microchip-pic-avr-examples/pic16f17146-cold-plate-mplab-mcc/pic16f17146-cold-plate-mplab-mcc.X/compactPrint.c

#include "compactPrint.h"

#include <xc.h>
#include "mcc_generated_files/system/system.h"
#include "fanControl.h"
#include "measurements.h"
#include "settings.h"
#include "peltierControl.h"
#include "currentSense.h"

//Sends a string of text to the UART with no newline appended
void compactPrint_sendStringLiteral(const char* str)
{
    uint8_t index = 0;
    while (str[index] != '\0')
    {
        if (UART1_IsTxReady())
        {
            UART1_Write(str[index]);
            index++;
        }
    }
    
    //Wait for TX
    while (!UART1_IsTxDone());
}

//Sends a string of text to the UART with a newline appended.
void compactPrint_sendStringWithNewline(const char* str)
{
    compactPrint_sendStringLiteral(str);
    compactPrint_sendStringLiteral("\r\n");
}

//Sends a string + error code with a newline appended.
void compactPrint_sendErrorCode(const char* str, uint8_t err)
{
    char buffer[4];
    
    //Send string
    compactPrint_sendStringLiteral(str);
    
    //Print Value
    compactPrint_convertUint8ToString(&buffer[0], err);
    compactPrint_sendStringWithNewline(buffer);
}

//Converts a duty cycle to a string
char* compactPrint_convertUint8ToString(char* str, uint8_t value)
{
    uint8_t divisor = 100;
    
    uint8_t index = 0, counter;
    bool hasStarted = false;
    while (divisor != 1)
    {
        //Reset iterative subtraction counter
        counter = 0;        
        while (divisor <= value)
        {
            //We started printing!
            hasStarted = true;
            
            //Subtract!
            value -= divisor;
            
            //Increment counter
            counter++;
        }
        
        if (hasStarted)
        {
            //We already printed a value!
            str[index] = '0' + counter;
            index++;
        }
        else
        {
            //Haven't printed anything, so leave it blank
            str[index] = ' ';
        }
        
        divisor /= 10;
    }
    
    //Last digit is always printed
    str[index] = value + '0';
    str[index + 1] = '\0';
    return (str + index + 1);
}

//Converts the value to a string. String contents are overwritten
char* compactPrint_convertUint16ToString(char* str, uint16_t value)
{
    uint16_t divisor = 10000;
    
    uint8_t index = 0, counter;
    bool hasStarted = false;
    while (divisor != 1)
    {
        //Reset iterative subtraction counter
        counter = 0;        
        while (divisor <= value)
        {
            //We started printing!
            hasStarted = true;
            
            //Subtract!
            value -= divisor;
            
            //Increment counter
            counter++;
        }
        
        if (hasStarted)
        {
            //We already printed a value!
            str[index] = '0' + counter;
            index++;
        }
        else
        {
            //Haven't printed anything, so leave it blank
            str[index] = ' ';
        }
        
        divisor /= 10;
    }
    
    //Last digit is always printed
    str[index] = value + '0';
    str[index + 1] = '\0';
    return (str + index + 1);
}

//Converts a temperature to a string with sign + unit
void compactPrint_convertTempToString(char* str, int8_t temp, char unit)
{
    uint8_t unsignTemp;
    
    if (temp < 0)
    {
        unsignTemp = temp * -1;
        str[0] = '-';
    }
    else
    {
        unsignTemp = temp;
        str[0] = '+';
    }
    
    //Convert temp to string
    char* end = compactPrint_convertUint8ToString((str + 1), unsignTemp);
    
    //Append unit
    *end = unit;
    *(end + 1) = '\0';
}

//Converts a current (in 100s of mA) to a string
void compactPrint_convertCurrentToString(char* str, uint8_t current)
{
    //10's digit
    char value = '0';
    while (current >= 100)
    {
        current -= 100;
        value++;
    }
    str[0] = value;
    
    //1's digit
    value = '0';
    while (current >= 10)
    {
        current -= 10;
        value++;
    }
    
    str[1] = value;
    str[2] = '.';
    
    //100mA digit
    str[3] = '0' + current;
    str[4] = 'A';
    str[5] = '\0';
}

//Sends Debug Telemetry to the UART
void compactPrint_sendDebugTelemetry(void)
{
    //Buffer for RPM/Temp/Etc...
    char buffer[6];
    
    compactPrint_sendStringWithNewline("--BEGIN TELEMETRY--");
        
    //If there is an error
    if (peltierControl_getError() != PELTIER_ERROR_NONE)
    {
        compactPrint_sendErrorCode("Peltier Control Error: ", peltierControl_getError());
    }
    
    compactPrint_sendStringLiteral("Peltier State: ");
    PeltierState currentPeltierState = peltierControl_getState();
    
    switch (currentPeltierState)
    {
        case PELTIER_STATE_DISABLED:
        {
            compactPrint_sendStringWithNewline("Disabled");
            break;
        }
        case PELTIER_STATE_STARTUP:
        {
            compactPrint_sendStringWithNewline("Startup");
            break;
        }
        case PELTIER_STATE_AT_TEMP:
        {
            compactPrint_sendStringWithNewline("At Temp");
            break;
        }
        case PELTIER_STATE_COOLING:
        {
            compactPrint_sendStringWithNewline("Cooling");
            break;
        }
        default:
        {
            compactPrint_sendStringWithNewline("Unknown");
        }
    }
    
    //Print Peltier Current
    compactPrint_sendStringLiteral("Peltier Current: ");
    compactPrint_convertCurrentToString(buffer, Measurements_getLastCurrent());
    compactPrint_sendStringWithNewline(buffer);
    
    compactPrint_sendStringLiteral("Peltier OCP Triggered: ");
    if (currentSense_hasOvercurrentOccurred())
    {
        compactPrint_sendStringWithNewline("TRUE");
    }
    else
    {
        compactPrint_sendStringWithNewline("FALSE");
    }
    
    //Print Fan 1 RPM
    compactPrint_sendStringLiteral("Fan 1 RPM: ");
    compactPrint_convertUint16ToString(buffer, fanControl_getFan1RPM());
    compactPrint_sendStringWithNewline(buffer);

    //Print Fan 2 RPM
    compactPrint_sendStringLiteral("Fan 2 RPM: ");
    compactPrint_convertUint16ToString(buffer, fanControl_getFan2RPM());
    compactPrint_sendStringWithNewline(buffer);

    //Print Cold Plate Temperature
    compactPrint_sendStringLiteral("Cold Plate Temp: ");
    compactPrint_convertTempToString(buffer, Measurements_getLastColdTemp(), settings_getSetting(SETTINGS_TEMP_UNIT));
    compactPrint_sendStringWithNewline(buffer);
    
    //Print Heatsink Temperature
    compactPrint_sendStringLiteral("Heatsink Temp: ");
    compactPrint_convertTempToString(buffer, Measurements_getLastHotTemp(), settings_getSetting(SETTINGS_TEMP_UNIT));
    compactPrint_sendStringWithNewline(buffer);

    //Print MCU Temperature
    compactPrint_sendStringLiteral("Int Temp: ");
    compactPrint_convertTempToString(buffer, Measurements_getLastIntTemp(), settings_getSetting(SETTINGS_TEMP_UNIT));
    compactPrint_sendStringWithNewline(buffer);
        
    compactPrint_sendStringWithNewline("--END TELEMETRY--\r\n");
}

//Sends Raw ADC values to the UART
void compactPrint_sendRawValues(void)
{
    char buffer[6];
    
    compactPrint_sendStringWithNewline("--BEGIN RAW DATA--");
    
    compactPrint_sendStringLiteral("Cold Sense ADC: ");
    compactPrint_convertUint16ToString(buffer, Measurements_getRawColdValue());
    compactPrint_sendStringWithNewline(buffer);
    
    compactPrint_sendStringLiteral("Hot Sense ADC: ");
    compactPrint_convertUint16ToString(buffer, Measurements_getRawHotValue());
    compactPrint_sendStringWithNewline(buffer);

    compactPrint_sendStringLiteral("Int. Temp ADC: ");
    compactPrint_convertUint16ToString(buffer, Measurements_getRawIntValue());
    compactPrint_sendStringWithNewline(buffer);
    
    compactPrint_sendStringLiteral("Current Sense ADC: ");
    compactPrint_convertUint16ToString(buffer, Measurements_getRawCurrentValue());
    compactPrint_sendStringWithNewline(buffer);
    
    //OPAMP Gain Startup Test
    compactPrint_sendStringLiteral("OPAMP Gain Self-Test: ");
    if (currentSense_isGainOK())
    {
        compactPrint_sendStringWithNewline("PASS");
    }
    else
    {
        compactPrint_sendStringWithNewline("FAIL");
    }
    
    compactPrint_sendStringLiteral("Power Fail CMP State: ");
    if (POWER_FAIL_CMP_GetOutputStatus())
    {
        //Power Fail
        compactPrint_sendStringWithNewline("TRUE");
    }
    else
    {
        compactPrint_sendStringWithNewline("FALSE");
    }
    
    compactPrint_sendStringLiteral("Overcurrent CMP State: ");
    if (OVERCURRENT_CMP_GetOutputStatus())
    {
        //Power Fail
        compactPrint_sendStringWithNewline("TRUE");
    }
    else
    {
        compactPrint_sendStringWithNewline("FALSE");
    }
    
    compactPrint_sendStringWithNewline("--END RAW DATA--\r\n");
}
