microchip-pic-avr-examples/pic16f17146-cold-plate-mplab-mcc/pic16f17146-cold-plate-mplab-mcc.X/runningMenus.h

#ifndef RUNNINGMENUS_H
#define	RUNNINGMENUS_H

#ifdef	__cplusplus
extern "C" {
#endif

#include <stdbool.h>
#include "mcc_generated_files/system/system.h"
#include <xc.h>
#include "OLED.h"
#include "fanControl.h"
#include "measurements.h"
#include "settingMenus.h"
    
void runningMenus_runningSetup(void);
void runningMenus_runningUpdate(int16_t moves);

void runningMenus_errorSetup(void);
void runningMenus_errorUpdate(int16_t moves);


#ifdef	__cplusplus
}
#endif

#endif	/* RUNNINGMENUS_H */
