microchip-pic-avr-examples/pic16f17146-cold-plate-mplab-mcc/pic16f17146-cold-plate-mplab-mcc.X/testing.h

#ifndef TESTING_H
#define	TESTING_H

#ifdef	__cplusplus
extern "C" {
#endif

    //Software Test Pattern for the NTC ROM Search Algorithm
    void TEST_NTC_ROM(void);
        
#ifdef	__cplusplus
}
#endif

#endif	/* TESTING_H */
