microchip-pic-avr-examples/pic16f17146-cold-plate-mplab-mcc/pic16f17146-cold-plate-mplab-mcc.X/utility.h

#ifndef UTILITY_H
#define	UTILITY_H

#ifdef	__cplusplus
extern "C" {
#endif
    
#include <stdint.h>
    
    //Read a value from the DIA fields in the MCU
    uint16_t DIA_readValue(uint16_t address);
    
    //Prints the Reset Registers to the UART
    void System_printResetRegisters(void);
    
    //Enables the WWDT
    void WWDT_start(void);
    
    //Stops the WWDT
    void WWDT_stop(void);
    
    //Arms a WWDT Reset
    //Should not be called immediately before WWDT_reset
    void WWDT_armReset(void);

    //Resets the WWDT
    void WWDT_reset(void);
    
    //Converts Celsius to Fahrenheit
    int8_t CtoF(int8_t celsius);

    //Converts Fahrenheit to Celsius
    int8_t FtoC(int8_t fahrenheit);
    
    //Switches temperature units automatically for the UI
    int8_t dispTemp(int8_t temp);
    
#ifdef	__cplusplus
}
#endif

#endif	/* UTILITY_H */
